wj-zhe/awkb/firmware/36/rev3/matrix.c

/*
Copyright 2012-2018 Jun Wako, Jack Humbert, Yiancar

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
You should have received a copy of the GNU General Public License
along with this program.  If not, see <http://www.gnu.org/licenses/>.
*/
#include <stdint.h>
#include <stdbool.h>
#include <string.h>

#include "util.h"
#include "matrix.h"
#include "debounce.h"
#include "atomic_util.h"

#include "print.h"

// Configurations for split keyboard by default
#include "split_common/split_util.h"
#include "split_common/transactions.h"

#ifdef MATRIX_ROW_PINS_RIGHT
#    define SPLIT_MUTABLE_ROW
#else
#    define SPLIT_MUTABLE_ROW const
#endif
#ifdef MATRIX_COL_PINS_RIGHT
#    define SPLIT_MUTABLE_COL
#else
#    define SPLIT_MUTABLE_COL const
#endif

#ifndef MATRIX_INPUT_PRESSED_STATE
#    define MATRIX_INPUT_PRESSED_STATE 0
#endif

// #undef  MATRIX_ROWS_PER_HAND
// #define MATRIX_ROWS_PER_HAND (MATRIX_ROWS)

static SPLIT_MUTABLE_ROW pin_t row_pins[MATRIX_ROWS_PER_HAND] = MATRIX_ROW_PINS;
static SPLIT_MUTABLE_COL pin_t col_pins[MATRIX_COLS]   = MATRIX_COL_PINS;

// matrix state(1:on, 0:off)
extern matrix_row_t raw_matrix[MATRIX_ROWS]; // raw values
extern matrix_row_t matrix[MATRIX_ROWS];     // debounced values

extern uint8_t thisHand, thatHand;
// END: Configurations for split keyboard by default 

// user-defined overridable functions
__attribute__((weak)) void matrix_init_pins(void);
__attribute__((weak)) void matrix_read_cols_on_row(matrix_row_t current_matrix[], uint8_t current_row);

static inline void gpio_atomic_set_pin_output_low(pin_t pin) {
    ATOMIC_BLOCK_FORCEON {
        gpio_set_pin_output(pin);
        gpio_write_pin_low(pin);
    }
}

static inline void gpio_atomic_set_pin_output_high(pin_t pin) {
    ATOMIC_BLOCK_FORCEON {
        gpio_set_pin_output(pin);
        gpio_write_pin_high(pin);
    }
}

static inline void gpio_atomic_set_pin_input_high(pin_t pin) {
    ATOMIC_BLOCK_FORCEON {
        gpio_set_pin_input_high(pin);
    }
}

static inline uint8_t readMatrixPin(pin_t pin) {
    if (pin != NO_PIN) {
        return (gpio_read_pin(pin) == MATRIX_INPUT_PRESSED_STATE) ? 0 : 1;
    } else {
        return 1;
    }
}

// matrix code

static bool select_col(uint8_t col) {
    pin_t pin = col_pins[col];
    if (pin != NO_PIN) {
        gpio_atomic_set_pin_output_low(pin);
        return true;
    }
    return false;
}

static void unselect_col(uint8_t col) {
    pin_t pin = col_pins[col];
    if (pin != NO_PIN) {
#            ifdef MATRIX_UNSELECT_DRIVE_HIGH
        gpio_atomic_set_pin_output_high(pin);
#            else
        gpio_atomic_set_pin_input_high(pin);
#            endif
    }
}

static void unselect_cols(void) {
    for (uint8_t x = 0; x < MATRIX_COLS; x++) {
        unselect_col(x);
    }
}

__attribute__((weak)) void matrix_init_pins(void) {
    unselect_cols();
    for (uint8_t x = 0; x < MATRIX_ROWS_PER_HAND; x++) {
        if (row_pins[x] != NO_PIN) {
            gpio_atomic_set_pin_input_high(row_pins[x]);
        }
    }
}

__attribute__((weak)) void matrix_read_rows_on_col(matrix_row_t current_matrix[], uint8_t current_col, matrix_row_t row_shifter) {
    bool key_pressed = false;

    // Select col
    if (!select_col(current_col)) { // select col
        return;                     // skip NO_PIN col
    }
    matrix_output_select_delay();

    // For each row...
    for (uint8_t row_index = 0; row_index < MATRIX_ROWS_PER_HAND; row_index++) {
        if (row_index == current_col) {
            continue;
        }

        // Check row pin state
        if (readMatrixPin(row_pins[row_index]) == 0) {
            // Pin LO, set col bit
            current_matrix[row_index] |= row_shifter;
            key_pressed = true;
        } else {
            // Pin HI, clear col bit
            current_matrix[row_index] &= ~row_shifter;
        }
    
    }

    // Unselect col
    unselect_col(current_col);
    matrix_output_unselect_delay(current_col, key_pressed); // wait for all Row signals to go HIGH
}

void matrix_init_custom(void) {
    // Config for split keyboard by default
    // Set pinout for right half if pinout for that half is defined
    if (!isLeftHand) {

#    ifdef MATRIX_ROW_PINS_RIGHT
        const pin_t row_pins_right[MATRIX_ROWS_PER_HAND] = MATRIX_ROW_PINS_RIGHT;
        for (uint8_t i = 0; i < MATRIX_ROWS_PER_HAND; i++) {
            row_pins[i] = row_pins_right[i];
        }
#    endif
#    ifdef MATRIX_COL_PINS_RIGHT
        const pin_t col_pins_right[MATRIX_COLS] = MATRIX_COL_PINS_RIGHT;
        for (uint8_t i = 0; i < MATRIX_COLS; i++) {
            col_pins[i] = col_pins_right[i];
        }
#    endif
    }

    thisHand = isLeftHand ? 0 : (MATRIX_ROWS_PER_HAND);
    thatHand = MATRIX_ROWS_PER_HAND - thisHand;
    // END: config for split keyboard

    // initialize key pins
    matrix_init_pins();

    // initialize matrix state: all keys off
    memset(matrix, 0, sizeof(matrix));
    memset(raw_matrix, 0, sizeof(raw_matrix));

    debounce_init();

    matrix_init_kb();
}

#ifdef SPLIT_KEYBOARD
// Fallback implementation for keyboards not using the standard split_util.c
__attribute__((weak)) bool transport_master_if_connected(matrix_row_t master_matrix[], matrix_row_t slave_matrix[]) {
    transport_master(master_matrix, slave_matrix);
    return true; // Treat the transport as always connected
}
#endif

uint8_t matrix_scan_custom(void) {
    // Common variables
    matrix_row_t curr_matrix[MATRIX_ROWS] = {0};

    // Set col, read rows
    matrix_row_t row_shifter = MATRIX_ROW_SHIFTER;
    for (uint8_t current_col = 0; current_col < MATRIX_COLS; current_col++, row_shifter <<= 1) {
        matrix_read_rows_on_col(curr_matrix, current_col, row_shifter);
    }

    // For split keyboard
    bool changed = memcmp(raw_matrix, curr_matrix, sizeof(curr_matrix)) != 0;
    if (changed) memcpy(raw_matrix, curr_matrix, sizeof(curr_matrix));

    changed = debounce(raw_matrix, matrix + thisHand, changed) | matrix_post_scan();

    return (uint8_t)changed;

}
