wj-zhe/awkb/firmware/36/rev3/keymaps/fsr_trackball/combo.h

// Layer 0 //
const uint16_t PROGMEM eql_combo[]       = { LGUI_T(KC_Q), KC_W, COMBO_END};
const uint16_t PROGMEM quot_combo[]      = { KC_I, KC_O, COMBO_END};
const uint16_t PROGMEM mins_combo[]      = { KC_O, LGUI_T(KC_P), COMBO_END};
const uint16_t PROGMEM plus_combo[]      = { KC_W, KC_D, COMBO_END};
const uint16_t PROGMEM lbrc_combo[]      = { KC_E, KC_F, COMBO_END};
const uint16_t PROGMEM lcbr_combo[]      = { KC_R, KC_G, COMBO_END};
const uint16_t PROGMEM rcbr_combo[]      = { KC_U, KC_H, COMBO_END};
const uint16_t PROGMEM rbrc_combo[]      = { KC_I, KC_J, COMBO_END};
const uint16_t PROGMEM unds_combo[]      = { KC_O, KC_K, COMBO_END};
const uint16_t PROGMEM caps_combo[]      = { KC_S, KC_D, COMBO_END};
const uint16_t PROGMEM dquo_combo[]      = { KC_L, LCTL_T(KC_SCLN), COMBO_END};
const uint16_t PROGMEM tild_combo[]      = { LSFT_T(KC_Z), KC_X, COMBO_END};
const uint16_t PROGMEM grv_combo[]       = { KC_X, KC_C, COMBO_END};
const uint16_t PROGMEM del_combo[]       = { LT(2,KC_TAB), LALT_T(KC_BSPC), COMBO_END};
const uint16_t PROGMEM bsls_combo[]      = { KC_COMM, KC_DOT, COMBO_END};
const uint16_t PROGMEM pipe_combo[]      = { KC_DOT, LSFT_T(KC_SLSH), COMBO_END};
const uint16_t PROGMEM td_md_ult_combo[] = { LALT_T(KC_SPC), TD(TD_L1), COMBO_END};

// Layer 3 //
const uint16_t PROGMEM qk_boot_combo[] = { LCTL_T(KC_END), LCTL_T(KC_PPLS), COMBO_END};
// const uint16_t PROGMEM qk_reboot_combo[] = { KC_PGDN, KC_PAST, COMBO_END}; // Resets the keyboard. Does not load the bootloader
const uint16_t PROGMEM ee_clr_combo[] = { KC_DOWN, KC_P5, COMBO_END}; // Resets the keyboard. Does not load the bootloader

// Layer 0 + 2 //
const uint16_t PROGMEM tg2_L0_combo[] = { KC_J, KC_K, KC_L, COMBO_END};
const uint16_t PROGMEM tg2_L2_combo[] = { KC_DOWN, KC_UP, KC_RIGHT, COMBO_END};

// Layer 0 + 3 //
const uint16_t PROGMEM tg3_L0_combo[] = { KC_M, KC_COMM, KC_DOT, COMBO_END};
const uint16_t PROGMEM tg3_L3_combo[] = { KC_P1, KC_P2, KC_P3, COMBO_END};

// Layer 0 + 1 + 2 + 3 //
const uint16_t PROGMEM ent_L0_combo[]   = { KC_K, KC_L, COMBO_END};
const uint16_t PROGMEM ent_L1_combo[]   = { KC_8, KC_9, COMBO_END};
const uint16_t PROGMEM ent_L2_combo[]   = { KC_UP, KC_RIGHT, COMBO_END};
const uint16_t PROGMEM ent_L3_combo[]   = { KC_P5, KC_P6, COMBO_END};
const uint16_t PROGMEM esc_L0_combo[]   = { KC_W, KC_E, COMBO_END};
const uint16_t PROGMEM esc_L1_combo[]   = { KC_AT, KC_HASH, COMBO_END};
const uint16_t PROGMEM esc_L2_combo[]   = { KC_F10, KC_F11, COMBO_END};
const uint16_t PROGMEM esc_L3_combo[]   = { KC_P8, KC_P9, COMBO_END};
const uint16_t PROGMEM esc_L3_2_combo[] = { KC_HOME, KC_UP, COMBO_END};

combo_t key_combos[] = {
    COMBO(eql_combo, KC_EQL),
    COMBO(quot_combo, KC_QUOT),
    COMBO(mins_combo, KC_MINS),
    COMBO(plus_combo, KC_PLUS),
    COMBO(lbrc_combo, KC_LBRC),
    COMBO(lcbr_combo, KC_LCBR),
    COMBO(rcbr_combo, KC_RCBR),
    COMBO(rbrc_combo, KC_RBRC),
    COMBO(unds_combo, KC_UNDS),
    COMBO(caps_combo, KC_CAPS),
    COMBO(dquo_combo, KC_DQUO),
    COMBO(tild_combo, KC_TILD),
    COMBO(grv_combo, KC_GRV),
    COMBO(del_combo, KC_DEL),
    COMBO(bsls_combo, KC_BSLS),
    COMBO(pipe_combo, KC_PIPE),
    COMBO(td_md_ult_combo, TD(TD_MD)),

    COMBO(qk_boot_combo, QK_BOOT),
    // COMBO(qk_reboot_combo, QK_RBT),
    COMBO(ee_clr_combo, EE_CLR),

    COMBO(tg2_L0_combo, TG(2)),
    COMBO(tg2_L2_combo, TG(2)),

    COMBO(tg3_L0_combo, TG(3)),
    COMBO(tg3_L3_combo, TG(3)),

    COMBO(ent_L0_combo, KC_ENT),
    COMBO(ent_L1_combo, KC_ENT),
    COMBO(ent_L2_combo, KC_ENT),
    COMBO(ent_L3_combo, KC_ENT),
    COMBO(esc_L0_combo, KC_ESC),
    COMBO(esc_L1_combo, KC_ESC),
    COMBO(esc_L2_combo, KC_ESC),
    COMBO(esc_L3_combo, KC_ESC),
    COMBO(esc_L3_2_combo, KC_ESC),

};


#ifdef COMBO_TERM_PER_COMBO
uint16_t get_combo_term(uint16_t combo_index, combo_t *combo) {
    // decide by combo->keycode
    switch (combo->keycode) {
        case KC_CAPS:
            return 75;
        case KC_LBRC: case KC_LCBR: case KC_RCBR: case KC_RBRC:
            return 40;

    }

    return COMBO_TERM;
}
#endif
